JoelKuula/Suspension_telemetry_public/pictures/USB-power-bank supply.jpg

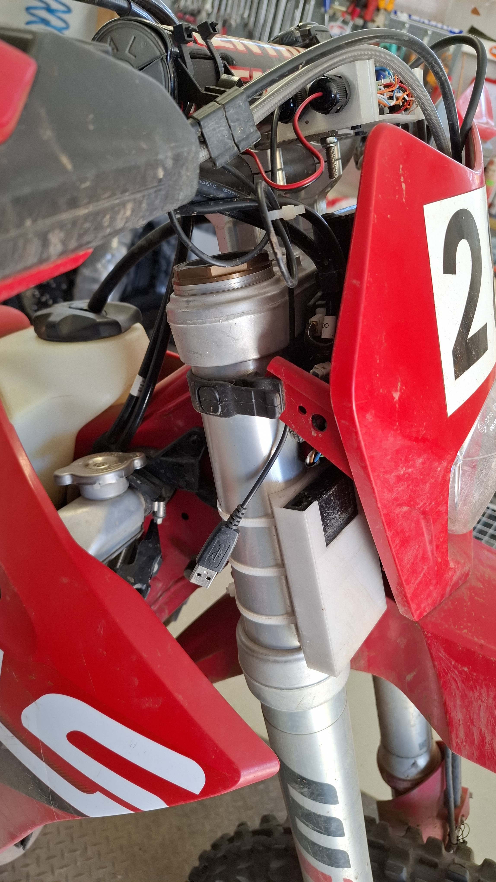
pictures/USB-power-bank supply.jpg
