JoelKuula/Suspension_telemetry_public/pictures/workbench-example-1.png

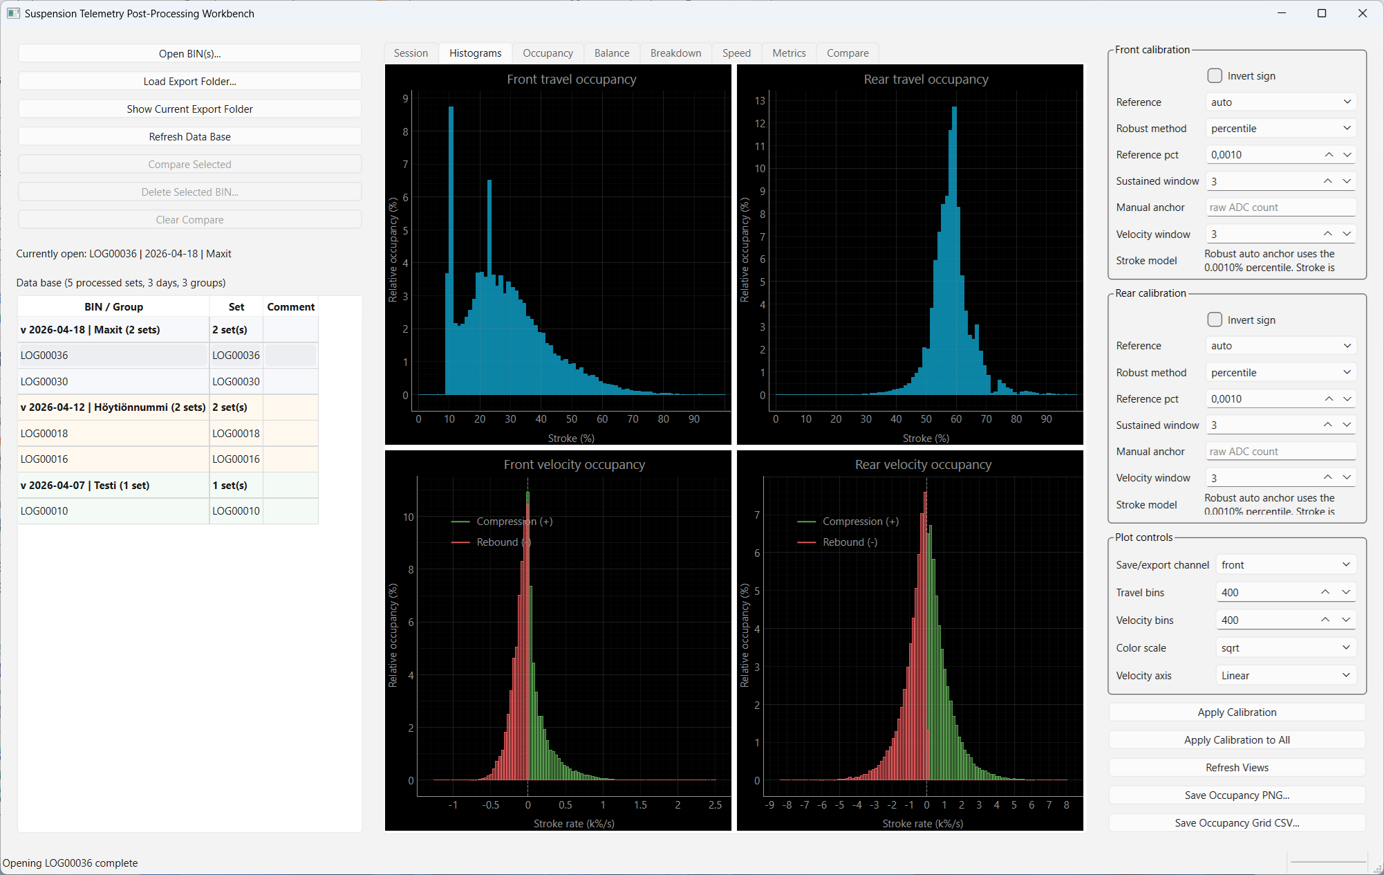
pictures/workbench-example-1.png
