JoelKuula/Suspension_telemetry_public/pictures/workbench-example-3.png

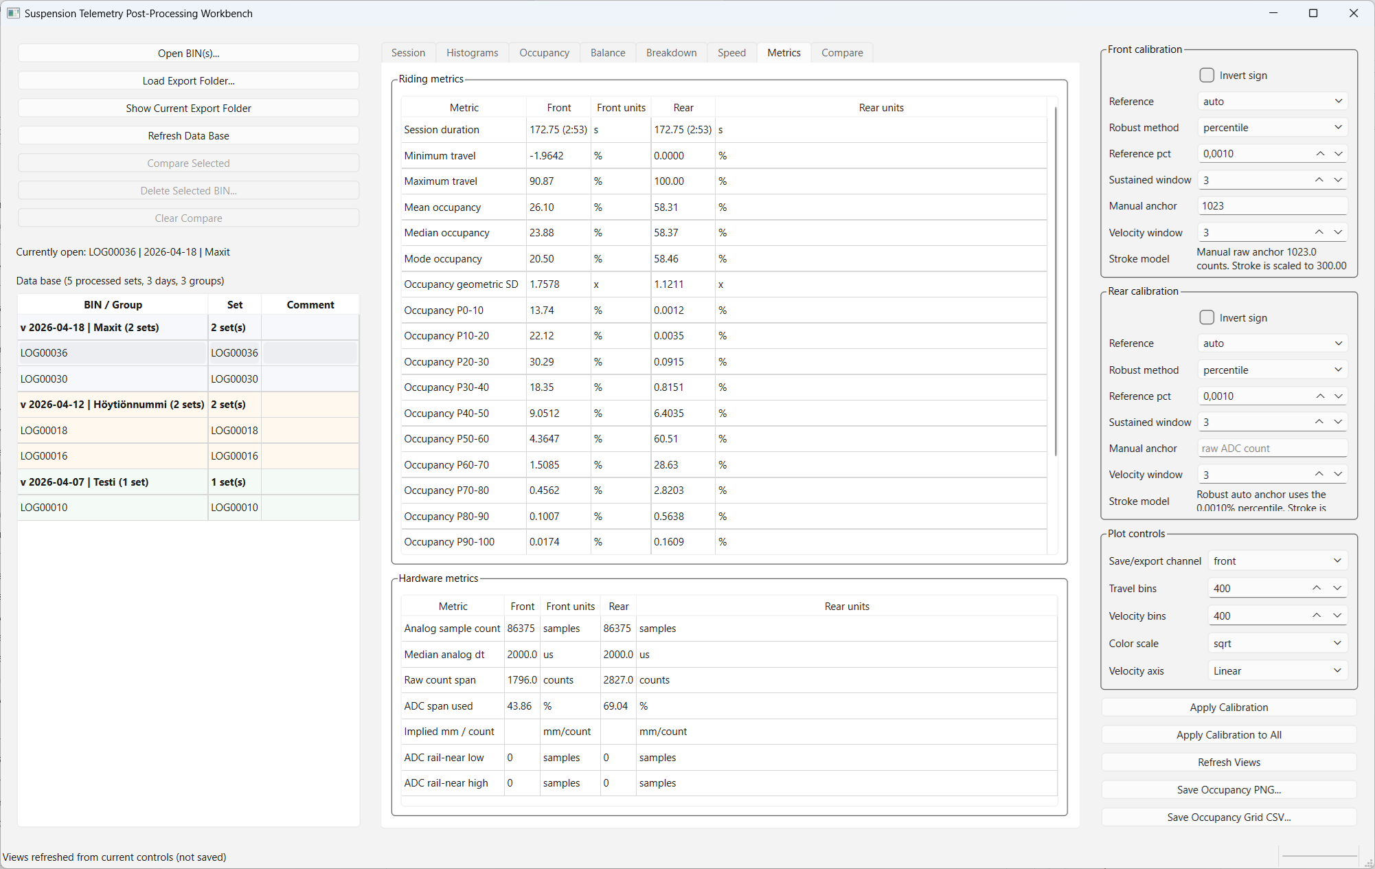
pictures/workbench-example-3.png
