JoelKuula/Suspension_telemetry_public/pictures/bom-2.jpg

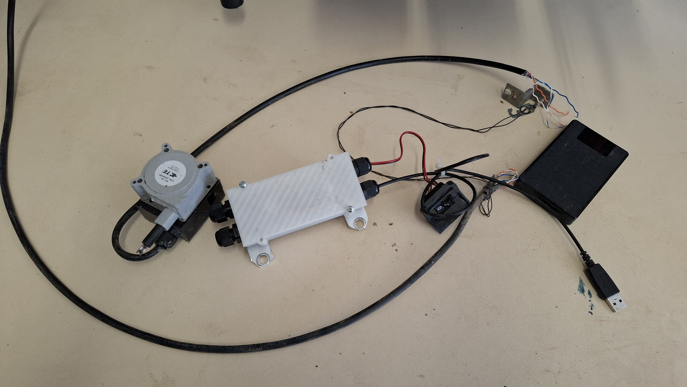
pictures/bom-2.jpg
